IbrahimOladepo/USB_PCIE_Board/2D/Photos/20260912_144538.jpg

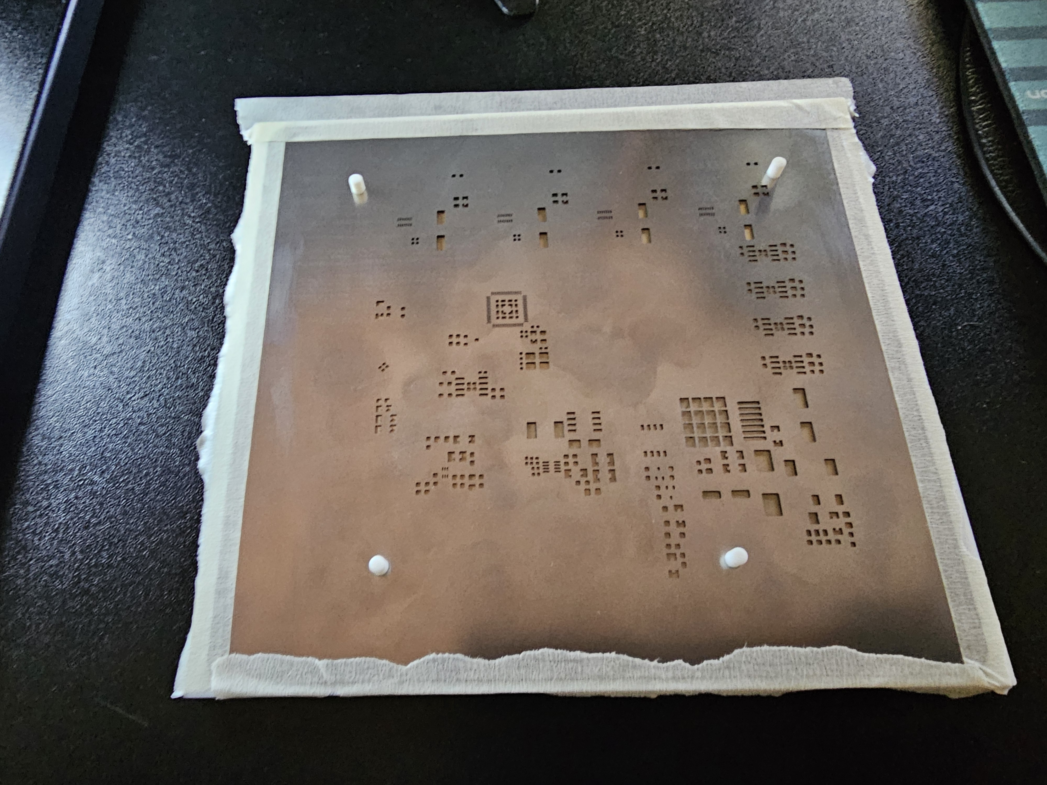
2D/Photos/20260912_144538.jpg
