IbrahimOladepo/USB_PCIE_Board/2D/Photos/20260912_221434.jpg

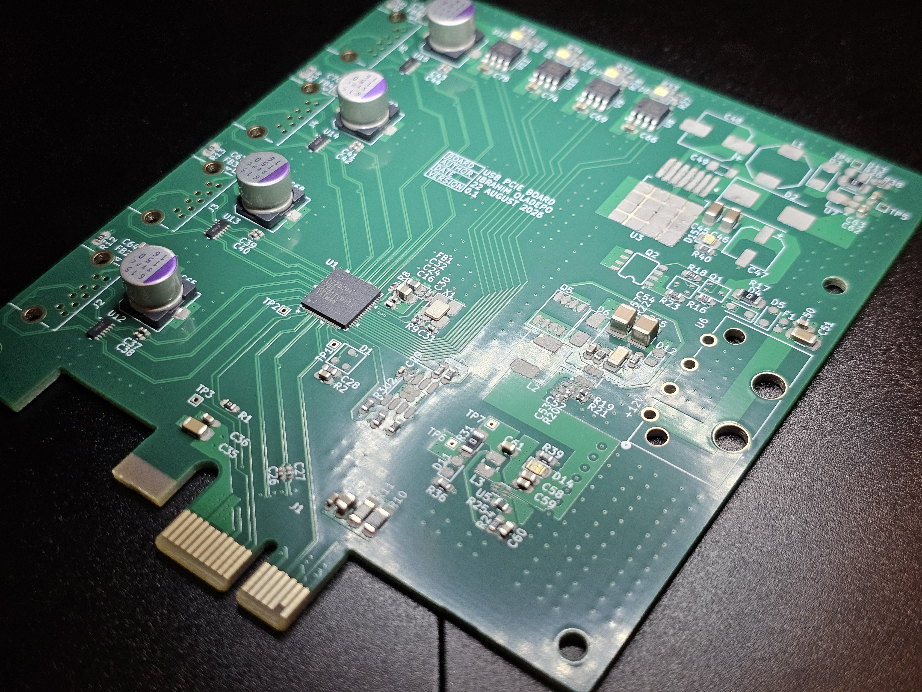
2D/Photos/20260912_221434.jpg
