IbrahimOladepo/USB_PCIE_Board/2D/Photos/20260913_112742.jpg

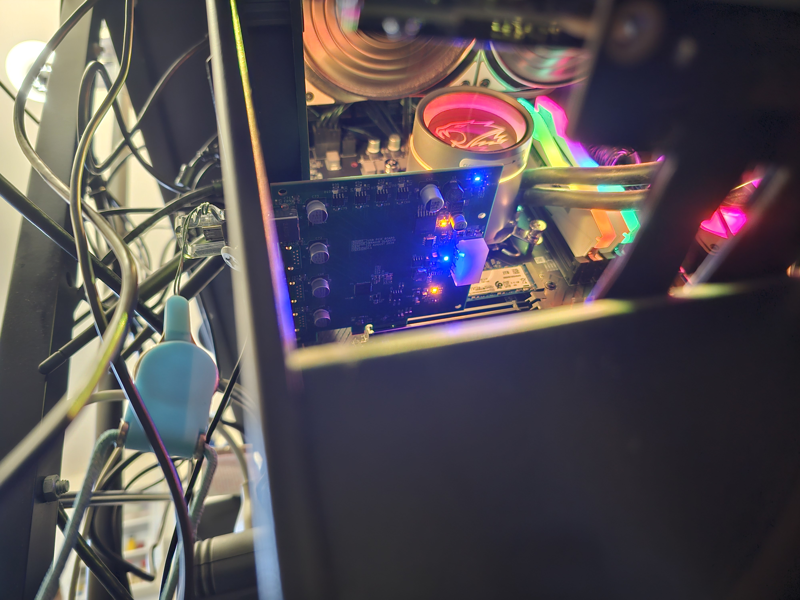
2D/Photos/20260913_112742.jpg
