IbrahimOladepo/USB_PCIE_Board/2D/Photos/20260913_144302.jpg

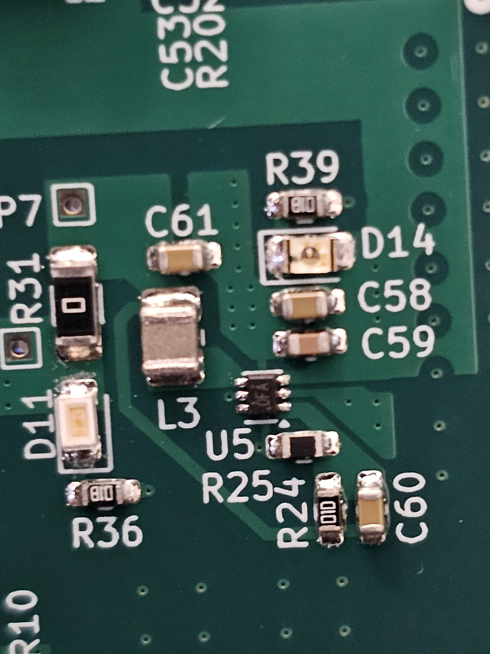
2D/Photos/20260913_144302.jpg
