IbrahimOladepo/USB_PCIE_Board/2D/Photos/20260916_135901.jpg

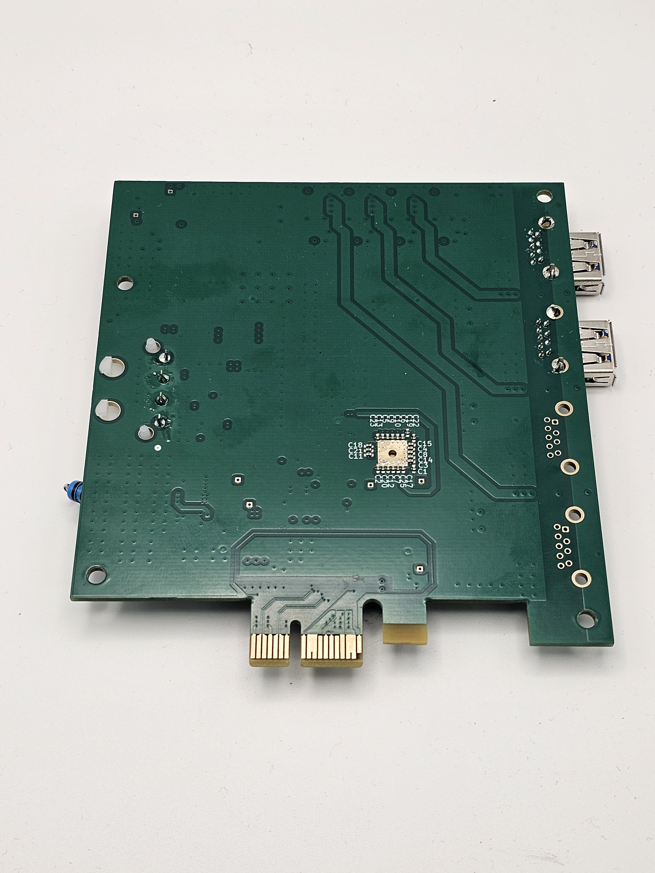
2D/Photos/20260916_135901.jpg
