IbrahimOladepo/USB_PCIE_Board/3D/USB_PCIE_Board_Blender_Render_02.png

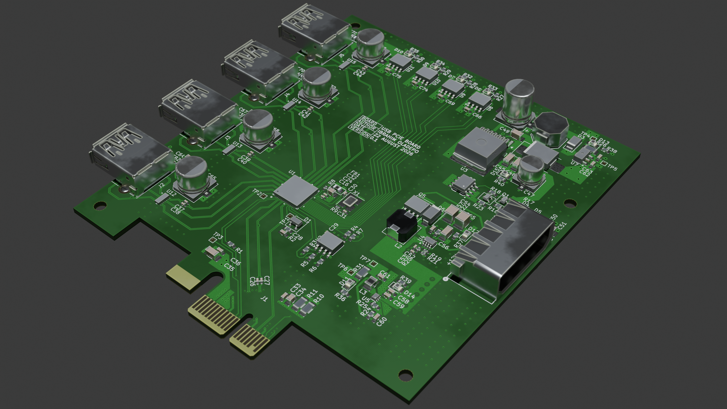
3D/USB_PCIE_Board_Blender_Render_02.png
