IbrahimOladepo/USB_PCIE_Board/3D/USB_PCIE_Board_Bottom.png

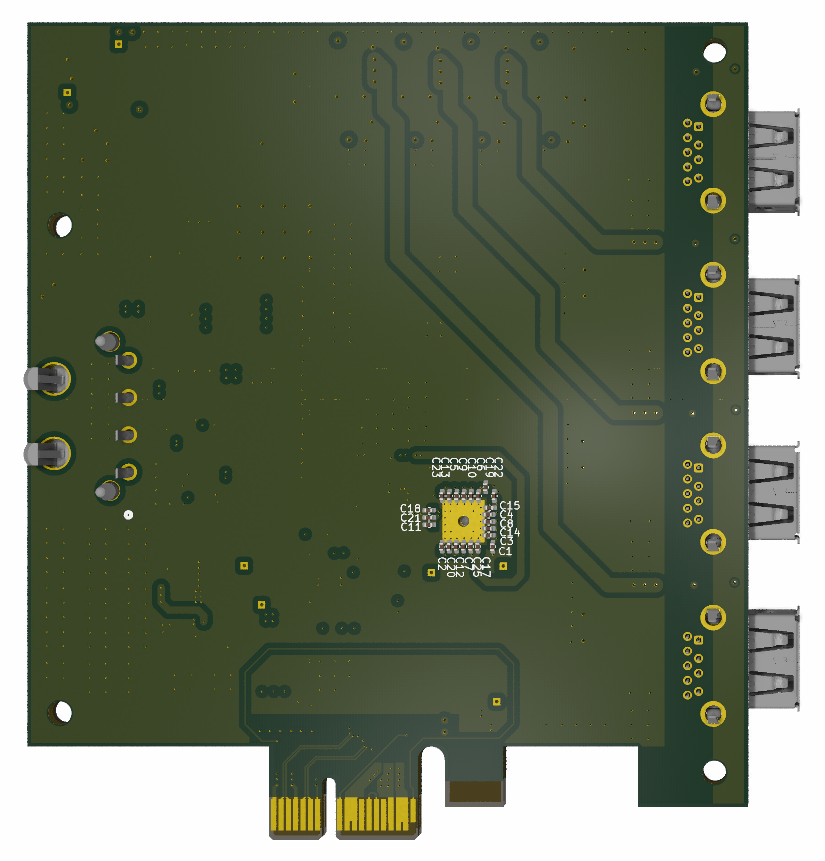
3D/USB_PCIE_Board_Bottom.png
