IbrahimOladepo/USB_PCIE_Board/2D/Photos/20260913_161005.jpg

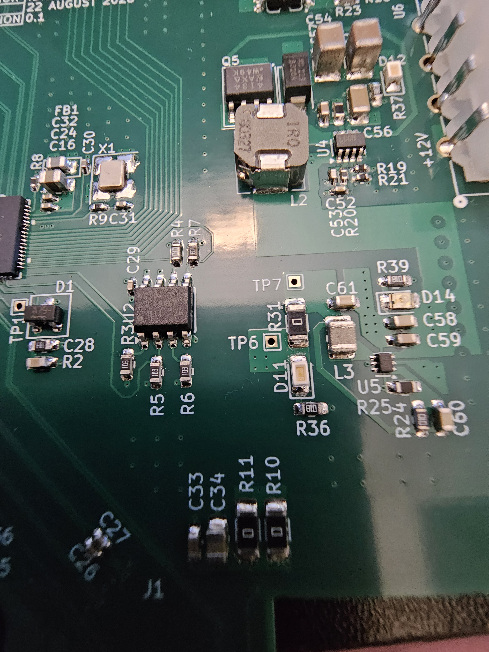
2D/Photos/20260913_161005.jpg
