IbrahimOladepo/USB_PCIE_Board/2D/Photos/20260914_095536.jpg

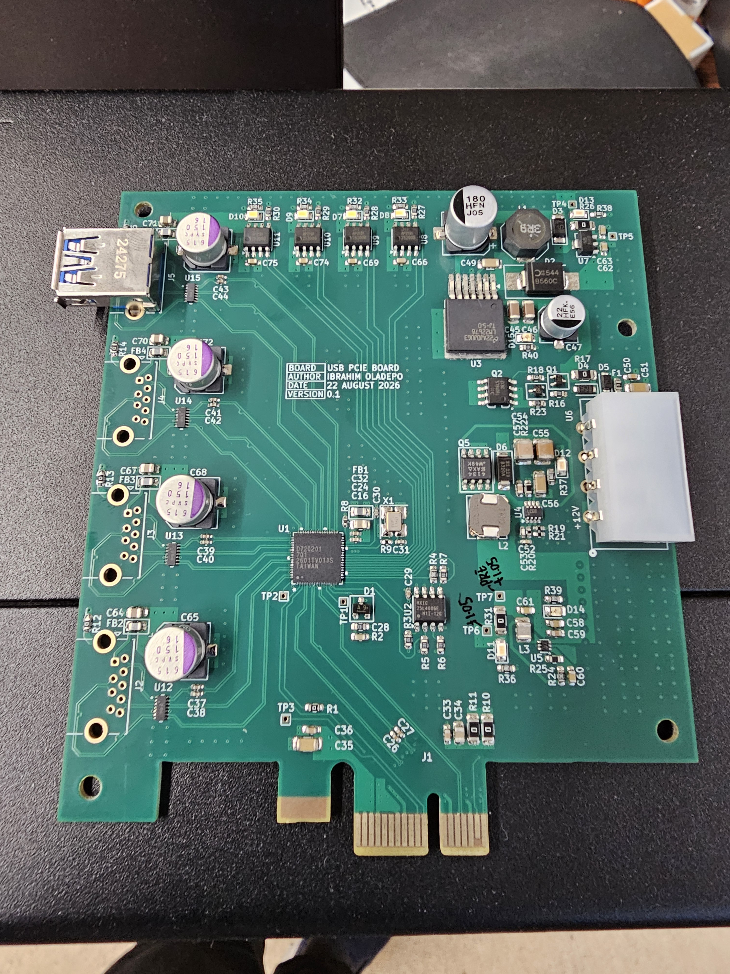
2D/Photos/20260914_095536.jpg
