IbrahimOladepo/USB_PCIE_Board/2D/Photos/20260914_095543.jpg

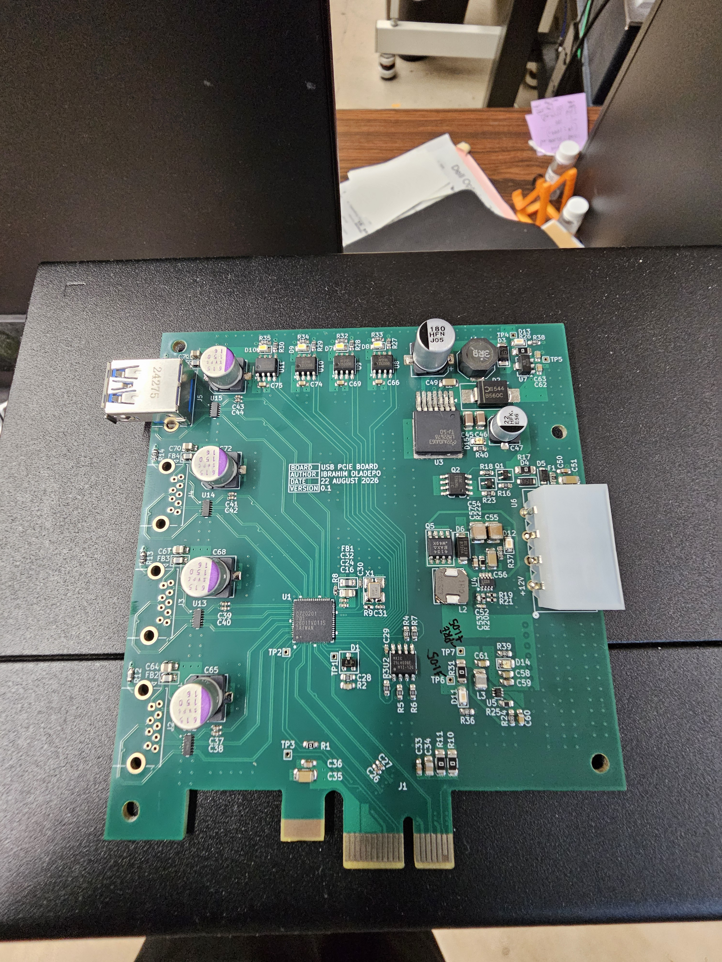
2D/Photos/20260914_095543.jpg
