IbrahimOladepo/USB_PCIE_Board/2D/Photos/20260914_095625.jpg

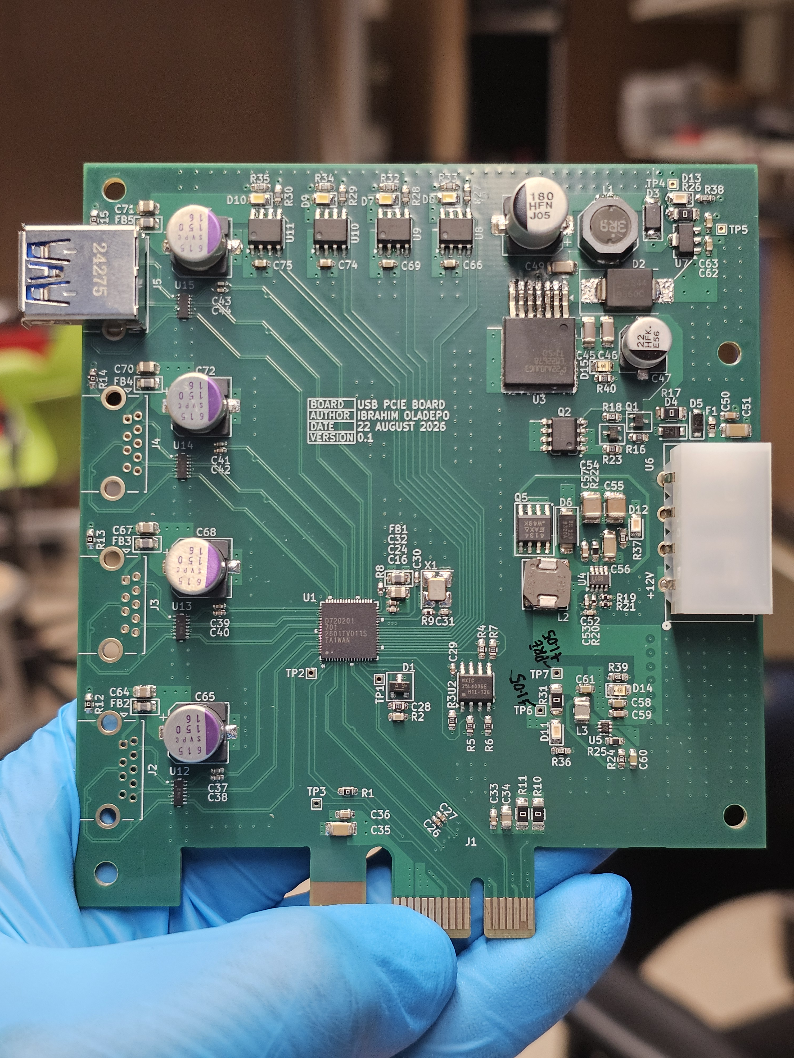
2D/Photos/20260914_095625.jpg
