IbrahimOladepo/USB_PCIE_Board/2D/Photos/20260920_213102.jpg

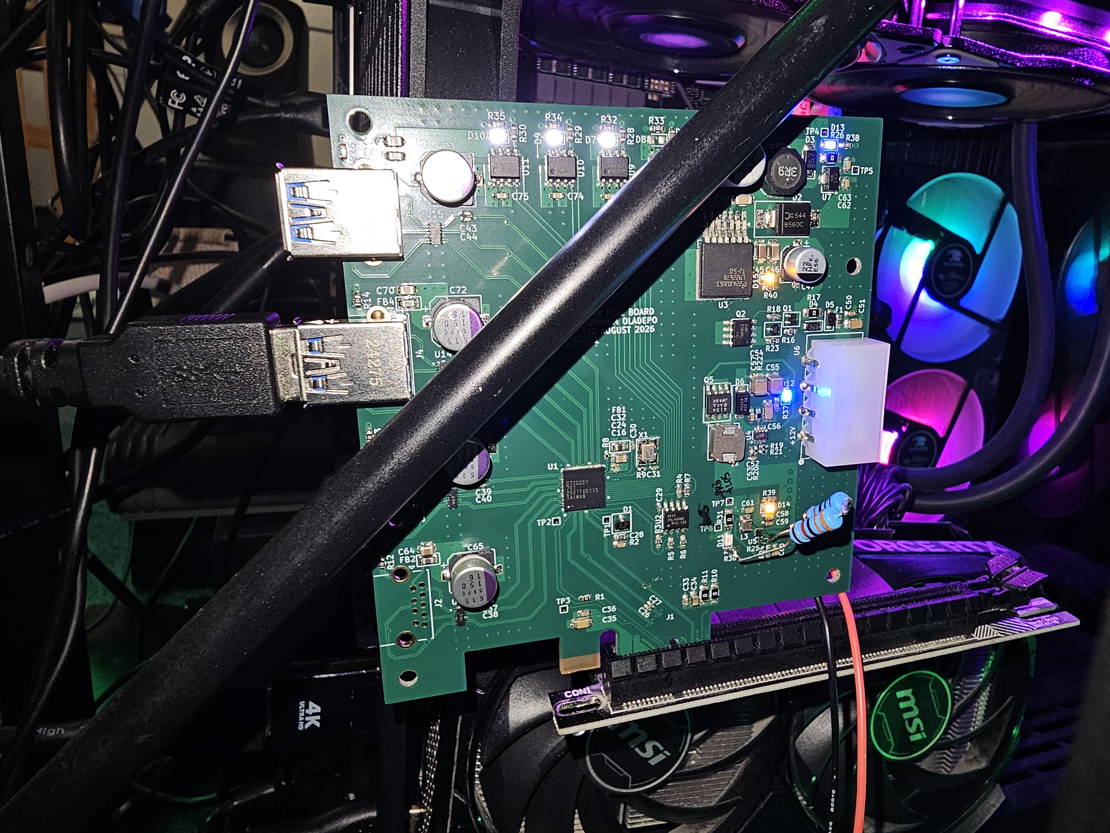
2D/Photos/20260920_213102.jpg
